Klafyvel/Trace/PCInterface/user_interface.py

# -*- coding: utf-8 -*-

# Form implementation generated from reading ui file 'window.ui'
#
# Created by: PyQt5 UI code generator 5.4.1
#
# WARNING! All changes made in this file will be lost!

from PyQt5 import QtCore, QtGui, QtWidgets

class Ui_MainWindow(object):
    def setupUi(self, MainWindow):
        MainWindow.setObjectName("MainWindow")
        MainWindow.resize(886, 528)
        icon = QtGui.QIcon()
        icon.addPixmap(QtGui.QPixmap("traceIcon.svg"), QtGui.QIcon.Normal, QtGui.QIcon.Off)
        MainWindow.setWindowIcon(icon)
        MainWindow.setTabShape(QtWidgets.QTabWidget.Triangular)
        self.centralwidget = QtWidgets.QWidget(MainWindow)
        self.centralwidget.setObjectName("centralwidget")
        self.verticalLayout_4 = QtWidgets.QVBoxLayout(self.centralwidget)
        self.verticalLayout_4.setObjectName("verticalLayout_4")
        self.tabWidget_2 = QtWidgets.QTabWidget(self.centralwidget)
        self.tabWidget_2.setObjectName("tabWidget_2")
        self.tab_2 = QtWidgets.QWidget()
        self.tab_2.setObjectName("tab_2")
        self.verticalLayout_9 = QtWidgets.QVBoxLayout(self.tab_2)
        self.verticalLayout_9.setObjectName("verticalLayout_9")
        self.horizontalLayout = QtWidgets.QHBoxLayout()
        self.horizontalLayout.setObjectName("horizontalLayout")
        self.filename = QtWidgets.QLabel(self.tab_2)
        self.filename.setObjectName("filename")
        self.horizontalLayout.addWidget(self.filename)
        self.btn_file = QtWidgets.QPushButton(self.tab_2)
        icon1 = QtGui.QIcon()
        icon1.addPixmap(QtGui.QPixmap("load.png"), QtGui.QIcon.Normal, QtGui.QIcon.Off)
        self.btn_file.setIcon(icon1)
        self.btn_file.setObjectName("btn_file")
        self.horizontalLayout.addWidget(self.btn_file)
        self.btn_reload = QtWidgets.QPushButton(self.tab_2)
        icon2 = QtGui.QIcon()
        icon2.addPixmap(QtGui.QPixmap("reload.png"), QtGui.QIcon.Normal, QtGui.QIcon.Off)
        self.btn_reload.setIcon(icon2)
        self.btn_reload.setObjectName("btn_reload")
        self.horizontalLayout.addWidget(self.btn_reload)
        self.verticalLayout_9.addLayout(self.horizontalLayout)
        self.btn_preprocessor = QtWidgets.QPushButton(self.tab_2)
        icon3 = QtGui.QIcon()
        icon3.addPixmap(QtGui.QPixmap("work.png"), QtGui.QIcon.Normal, QtGui.QIcon.Off)
        self.btn_preprocessor.setIcon(icon3)
        self.btn_preprocessor.setObjectName("btn_preprocessor")
        self.verticalLayout_9.addWidget(self.btn_preprocessor)
        self.widget_2 = QtWidgets.QWidget(self.tab_2)
        self.widget_2.setObjectName("widget_2")
        self.horizontalLayout_5 = QtWidgets.QHBoxLayout(self.widget_2)
        self.horizontalLayout_5.setContentsMargins(0, 0, 0, 0)
        self.horizontalLayout_5.setObjectName("horizontalLayout_5")
        self.widget = QtWidgets.QWidget(self.widget_2)
        self.widget.setObjectName("widget")
        self.verticalLayout_5 = QtWidgets.QVBoxLayout(self.widget)
        self.verticalLayout_5.setContentsMargins(0, 0, 0, 0)
        self.verticalLayout_5.setObjectName("verticalLayout_5")
        self.fileview = QtWidgets.QGraphicsView(self.widget)
        self.fileview.setSizeAdjustPolicy(QtWidgets.QAbstractScrollArea.AdjustToContents)
        self.fileview.setDragMode(QtWidgets.QGraphicsView.ScrollHandDrag)
        self.fileview.setObjectName("fileview")
        self.verticalLayout_5.addWidget(self.fileview)
        self.widget_5 = QtWidgets.QWidget(self.widget)
        self.widget_5.setObjectName("widget_5")
        self.horizontalLayout_8 = QtWidgets.QHBoxLayout(self.widget_5)
        self.horizontalLayout_8.setContentsMargins(0, 0, 0, 0)
        self.horizontalLayout_8.setObjectName("horizontalLayout_8")
        self.display_draw_steps = QtWidgets.QCheckBox(self.widget_5)
        self.display_draw_steps.setObjectName("display_draw_steps")
        self.horizontalLayout_8.addWidget(self.display_draw_steps)
        self.redraw = QtWidgets.QPushButton(self.widget_5)
        icon4 = QtGui.QIcon()
        icon4.addPixmap(QtGui.QPixmap("writing.png"), QtGui.QIcon.Normal, QtGui.QIcon.Off)
        self.redraw.setIcon(icon4)
        self.redraw.setObjectName("redraw")
        self.horizontalLayout_8.addWidget(self.redraw)
        self.verticalLayout_5.addWidget(self.widget_5)
        self.horizontalLayout_5.addWidget(self.widget)
        self.widget_3 = QtWidgets.QWidget(self.widget_2)
        self.widget_3.setObjectName("widget_3")
        self.verticalLayout = QtWidgets.QVBoxLayout(self.widget_3)
        self.verticalLayout.setContentsMargins(0, 0, 0, 0)
        self.verticalLayout.setObjectName("verticalLayout")
        self.code_edit = QtWidgets.QTextEdit(self.widget_3)
        self.code_edit.setObjectName("code_edit")
        self.verticalLayout.addWidget(self.code_edit)
        self.widget_4 = QtWidgets.QWidget(self.widget_3)
        self.widget_4.setObjectName("widget_4")
        self.horizontalLayout_7 = QtWidgets.QHBoxLayout(self.widget_4)
        self.horizontalLayout_7.setContentsMargins(0, 0, 0, 0)
        self.horizontalLayout_7.setObjectName("horizontalLayout_7")
        self.btn_save_file = QtWidgets.QPushButton(self.widget_4)
        icon5 = QtGui.QIcon()
        icon5.addPixmap(QtGui.QPixmap("save.png"), QtGui.QIcon.Normal, QtGui.QIcon.Off)
        self.btn_save_file.setIcon(icon5)
        self.btn_save_file.setObjectName("btn_save_file")
        self.horizontalLayout_7.addWidget(self.btn_save_file)
        self.btn_save_as = QtWidgets.QPushButton(self.widget_4)
        self.btn_save_as.setIcon(icon5)
        self.btn_save_as.setObjectName("btn_save_as")
        self.horizontalLayout_7.addWidget(self.btn_save_as)
        self.verticalLayout.addWidget(self.widget_4)
        self.horizontalLayout_5.addWidget(self.widget_3)
        self.verticalLayout_9.addWidget(self.widget_2)
        self.tabWidget_2.addTab(self.tab_2, "")
        self.tab_3 = QtWidgets.QWidget()
        self.tab_3.setObjectName("tab_3")
        self.horizontalLayout_2 = QtWidgets.QHBoxLayout(self.tab_3)
        self.horizontalLayout_2.setObjectName("horizontalLayout_2")
        self.groupBox = QtWidgets.QGroupBox(self.tab_3)
        self.groupBox.setObjectName("groupBox")
        self.verticalLayout_2 = QtWidgets.QVBoxLayout(self.groupBox)
        self.verticalLayout_2.setObjectName("verticalLayout_2")
        self.serial_monitor = QtWidgets.QTextEdit(self.groupBox)
        sizePolicy = QtWidgets.QSizePolicy(QtWidgets.QSizePolicy.Expanding, QtWidgets.QSizePolicy.Minimum)
        sizePolicy.setHorizontalStretch(0)
        sizePolicy.setVerticalStretch(0)
        sizePolicy.setHeightForWidth(self.serial_monitor.sizePolicy().hasHeightForWidth())
        self.serial_monitor.setSizePolicy(sizePolicy)
        self.serial_monitor.setMinimumSize(QtCore.QSize(0, 300))
        self.serial_monitor.setMaximumSize(QtCore.QSize(16777215, 2000))
        self.serial_monitor.setStyleSheet("background-color:black;")
        self.serial_monitor.setReadOnly(True)
        self.serial_monitor.setObjectName("serial_monitor")
        self.verticalLayout_2.addWidget(self.serial_monitor)
        self.horizontalLayout_4 = QtWidgets.QHBoxLayout()
        self.horizontalLayout_4.setObjectName("horizontalLayout_4")
        self.label_4 = QtWidgets.QLabel(self.groupBox)
        self.label_4.setObjectName("label_4")
        self.horizontalLayout_4.addWidget(self.label_4)
        self.command_edit = QtWidgets.QLineEdit(self.groupBox)
        self.command_edit.setObjectName("command_edit")
        self.horizontalLayout_4.addWidget(self.command_edit)
        self.btn_command = QtWidgets.QPushButton(self.groupBox)
        icon6 = QtGui.QIcon()
        icon6.addPixmap(QtGui.QPixmap("run.png"), QtGui.QIcon.Normal, QtGui.QIcon.Off)
        self.btn_command.setIcon(icon6)
        self.btn_command.setObjectName("btn_command")
        self.horizontalLayout_4.addWidget(self.btn_command)
        self.verticalLayout_2.addLayout(self.horizontalLayout_4)
        self.horizontalLayout_2.addWidget(self.groupBox)
        self.tabWidget = QtWidgets.QTabWidget(self.tab_3)
        self.tabWidget.setObjectName("tabWidget")
        self.tab_serie = QtWidgets.QWidget()
        self.tab_serie.setObjectName("tab_serie")
        self.verticalLayout_3 = QtWidgets.QVBoxLayout(self.tab_serie)
        self.verticalLayout_3.setObjectName("verticalLayout_3")
        self.chk_enableFakeSerial = QtWidgets.QCheckBox(self.tab_serie)
        self.chk_enableFakeSerial.setObjectName("chk_enableFakeSerial")
        self.verticalLayout_3.addWidget(self.chk_enableFakeSerial)
        self.trueSerialContainer = QtWidgets.QWidget(self.tab_serie)
        self.trueSerialContainer.setObjectName("trueSerialContainer")
        self.verticalLayout_10 = QtWidgets.QVBoxLayout(self.trueSerialContainer)
        self.verticalLayout_10.setContentsMargins(0, 0, 0, 0)
        self.verticalLayout_10.setObjectName("verticalLayout_10")
        self.serial_settings = QtWidgets.QFormLayout()
        self.serial_settings.setObjectName("serial_settings")
        self.label = QtWidgets.QLabel(self.trueSerialContainer)
        self.label.setObjectName("label")
        self.serial_settings.setWidget(0, QtWidgets.QFormLayout.LabelRole, self.label)
        self.baudrate = QtWidgets.QComboBox(self.trueSerialContainer)
        self.baudrate.setObjectName("baudrate")
        self.baudrate.addItem("")
        self.baudrate.addItem("")
        self.baudrate.addItem("")
        self.baudrate.addItem("")
        self.baudrate.addItem("")
        self.baudrate.addItem("")
        self.baudrate.addItem("")
        self.baudrate.addItem("")
        self.baudrate.addItem("")
        self.baudrate.addItem("")
        self.baudrate.addItem("")
        self.serial_settings.setWidget(0, QtWidgets.QFormLayout.FieldRole, self.baudrate)
        self.portSRieLabel = QtWidgets.QLabel(self.trueSerialContainer)
        self.portSRieLabel.setObjectName("portSRieLabel")
        self.serial_settings.setWidget(1, QtWidgets.QFormLayout.LabelRole, self.portSRieLabel)
        self.serial_ports_list = QtWidgets.QComboBox(self.trueSerialContainer)
        self.serial_ports_list.setObjectName("serial_ports_list")
        self.serial_settings.setWidget(1, QtWidgets.QFormLayout.FieldRole, self.serial_ports_list)
        self.btn_serial_ports_list = QtWidgets.QPushButton(self.trueSerialContainer)
        self.btn_serial_ports_list.setObjectName("btn_serial_ports_list")
        self.serial_settings.setWidget(2, QtWidgets.QFormLayout.FieldRole, self.btn_serial_ports_list)
        self.label_5 = QtWidgets.QLabel(self.trueSerialContainer)
        self.label_5.setObjectName("label_5")
        self.serial_settings.setWidget(3, QtWidgets.QFormLayout.LabelRole, self.label_5)
        self.timeout_read = QtWidgets.QSpinBox(self.trueSerialContainer)
        self.timeout_read.setMaximum(1000)
        self.timeout_read.setProperty("value", 10)
        self.timeout_read.setObjectName("timeout_read")
        self.serial_settings.setWidget(3, QtWidgets.QFormLayout.FieldRole, self.timeout_read)
        self.utiliserFichierLogTxtLabel = QtWidgets.QLabel(self.trueSerialContainer)
        self.utiliserFichierLogTxtLabel.setObjectName("utiliserFichierLogTxtLabel")
        self.serial_settings.setWidget(4, QtWidgets.QFormLayout.LabelRole, self.utiliserFichierLogTxtLabel)
        self.use_log = QtWidgets.QCheckBox(self.trueSerialContainer)
        self.use_log.setObjectName("use_log")
        self.serial_settings.setWidget(4, QtWidgets.QFormLayout.FieldRole, self.use_log)
        self.verticalLayout_10.addLayout(self.serial_settings)
        self.btn_connect = QtWidgets.QPushButton(self.trueSerialContainer)
        icon7 = QtGui.QIcon()
        icon7.addPixmap(QtGui.QPixmap("connect.png"), QtGui.QIcon.Normal, QtGui.QIcon.Off)
        self.btn_connect.setIcon(icon7)
        self.btn_connect.setObjectName("btn_connect")
        self.verticalLayout_10.addWidget(self.btn_connect)
        self.verticalLayout_3.addWidget(self.trueSerialContainer)
        self.tabWidget.addTab(self.tab_serie, "")
        self.tab = QtWidgets.QWidget()
        self.tab.setObjectName("tab")
        self.verticalLayout_8 = QtWidgets.QVBoxLayout(self.tab)
        self.verticalLayout_8.setObjectName("verticalLayout_8")
        self.send_manual_cmd = QtWidgets.QCheckBox(self.tab)
        self.send_manual_cmd.setObjectName("send_manual_cmd")
        self.verticalLayout_8.addWidget(self.send_manual_cmd)
        self.grp_plan = QtWidgets.QGroupBox(self.tab)
        self.grp_plan.setObjectName("grp_plan")
        self.verticalLayout_6 = QtWidgets.QVBoxLayout(self.grp_plan)
        self.verticalLayout_6.setObjectName("verticalLayout_6")
        self.gridLayout_2 = QtWidgets.QGridLayout()
        self.gridLayout_2.setObjectName("gridLayout_2")
        self.btn_y_plus = QtWidgets.QPushButton(self.grp_plan)
        icon8 = QtGui.QIcon()
        icon8.addPixmap(QtGui.QPixmap("up.png"), QtGui.QIcon.Normal, QtGui.QIcon.Off)
        self.btn_y_plus.setIcon(icon8)
        self.btn_y_plus.setObjectName("btn_y_plus")
        self.gridLayout_2.addWidget(self.btn_y_plus, 0, 1, 1, 1)
        self.btn_x_plus = QtWidgets.QPushButton(self.grp_plan)
        icon9 = QtGui.QIcon()
        icon9.addPixmap(QtGui.QPixmap("right.png"), QtGui.QIcon.Normal, QtGui.QIcon.Off)
        self.btn_x_plus.setIcon(icon9)
        self.btn_x_plus.setObjectName("btn_x_plus")
        self.gridLayout_2.addWidget(self.btn_x_plus, 1, 2, 1, 1)
        self.btn_y_minus = QtWidgets.QPushButton(self.grp_plan)
        icon10 = QtGui.QIcon()
        icon10.addPixmap(QtGui.QPixmap("down.png"), QtGui.QIcon.Normal, QtGui.QIcon.Off)
        self.btn_y_minus.setIcon(icon10)
        self.btn_y_minus.setObjectName("btn_y_minus")
        self.gridLayout_2.addWidget(self.btn_y_minus, 2, 1, 1, 1)
        self.label_6 = QtWidgets.QLabel(self.grp_plan)
        self.label_6.setObjectName("label_6")
        self.gridLayout_2.addWidget(self.label_6, 0, 3, 1, 1)
        self.btn_x_minus = QtWidgets.QPushButton(self.grp_plan)
        icon11 = QtGui.QIcon()
        icon11.addPixmap(QtGui.QPixmap("left.png"), QtGui.QIcon.Normal, QtGui.QIcon.Off)
        self.btn_x_minus.setIcon(icon11)
        self.btn_x_minus.setObjectName("btn_x_minus")
        self.gridLayout_2.addWidget(self.btn_x_minus, 1, 0, 1, 1)
        self.step_x = QtWidgets.QDoubleSpinBox(self.grp_plan)
        self.step_x.setPrefix("")
        self.step_x.setProperty("value", 1.0)
        self.step_x.setObjectName("step_x")
        self.gridLayout_2.addWidget(self.step_x, 0, 4, 1, 1)
        self.label_7 = QtWidgets.QLabel(self.grp_plan)
        self.label_7.setObjectName("label_7")
        self.gridLayout_2.addWidget(self.label_7, 2, 3, 1, 1)
        self.step_y = QtWidgets.QDoubleSpinBox(self.grp_plan)
        self.step_y.setProperty("value", 1.0)
        self.step_y.setObjectName("step_y")
        self.gridLayout_2.addWidget(self.step_y, 2, 4, 1, 1)
        self.verticalLayout_6.addLayout(self.gridLayout_2)
        self.verticalLayout_8.addWidget(self.grp_plan)
        self.horizontalLayout_3 = QtWidgets.QHBoxLayout()
        self.horizontalLayout_3.setObjectName("horizontalLayout_3")
        self.grp_z = QtWidgets.QGroupBox(self.tab)
        self.grp_z.setFlat(False)
        self.grp_z.setCheckable(False)
        self.grp_z.setObjectName("grp_z")
        self.horizontalLayout_6 = QtWidgets.QHBoxLayout(self.grp_z)
        self.horizontalLayout_6.setObjectName("horizontalLayout_6")
        self.btn_set_z_low = QtWidgets.QPushButton(self.grp_z)
        self.btn_set_z_low.setIcon(icon4)
        self.btn_set_z_low.setIconSize(QtCore.QSize(64, 64))
        self.btn_set_z_low.setObjectName("btn_set_z_low")
        self.horizontalLayout_6.addWidget(self.btn_set_z_low)
        self.btn_set_z_high = QtWidgets.QPushButton(self.grp_z)
        icon12 = QtGui.QIcon()
        icon12.addPixmap(QtGui.QPixmap("not_writing.png"), QtGui.QIcon.Normal, QtGui.QIcon.Off)
        self.btn_set_z_high.setIcon(icon12)
        self.btn_set_z_high.setIconSize(QtCore.QSize(64, 64))
        self.btn_set_z_high.setObjectName("btn_set_z_high")
        self.horizontalLayout_6.addWidget(self.btn_set_z_high)
        self.horizontalLayout_3.addWidget(self.grp_z)
        self.verticalLayout_8.addLayout(self.horizontalLayout_3)
        self.btn_go_to_zero = QtWidgets.QPushButton(self.tab)
        sizePolicy = QtWidgets.QSizePolicy(QtWidgets.QSizePolicy.Expanding, QtWidgets.QSizePolicy.Expanding)
        sizePolicy.setHorizontalStretch(0)
        sizePolicy.setVerticalStretch(0)
        sizePolicy.setHeightForWidth(self.btn_go_to_zero.sizePolicy().hasHeightForWidth())
        self.btn_go_to_zero.setSizePolicy(sizePolicy)
        icon13 = QtGui.QIcon()
        icon13.addPixmap(QtGui.QPixmap("origin.png"), QtGui.QIcon.Normal, QtGui.QIcon.Off)
        self.btn_go_to_zero.setIcon(icon13)
        self.btn_go_to_zero.setIconSize(QtCore.QSize(64, 64))
        self.btn_go_to_zero.setFlat(False)
        self.btn_go_to_zero.setObjectName("btn_go_to_zero")
        self.verticalLayout_8.addWidget(self.btn_go_to_zero)
        self.btn_send_current_file = QtWidgets.QPushButton(self.tab)
        icon14 = QtGui.QIcon()
        icon14.addPixmap(QtGui.QPixmap("upload.png"), QtGui.QIcon.Normal, QtGui.QIcon.Off)
        self.btn_send_current_file.setIcon(icon14)
        self.btn_send_current_file.setObjectName("btn_send_current_file")
        self.verticalLayout_8.addWidget(self.btn_send_current_file)
        self.tabWidget.addTab(self.tab, "")
        self.horizontalLayout_2.addWidget(self.tabWidget)
        self.tabWidget_2.addTab(self.tab_3, "")
        self.tab_4 = QtWidgets.QWidget()
        self.tab_4.setObjectName("tab_4")
        self.verticalLayout_7 = QtWidgets.QVBoxLayout(self.tab_4)
        self.verticalLayout_7.setObjectName("verticalLayout_7")
        self.label_2 = QtWidgets.QLabel(self.tab_4)
        self.label_2.setTextFormat(QtCore.Qt.RichText)
        self.label_2.setObjectName("label_2")
        self.verticalLayout_7.addWidget(self.label_2)
        self.textBrowser_2 = QtWidgets.QTextBrowser(self.tab_4)
        self.textBrowser_2.setObjectName("textBrowser_2")
        self.verticalLayout_7.addWidget(self.textBrowser_2)
        self.aboutQt = QtWidgets.QPushButton(self.tab_4)
        icon = QtGui.QIcon.fromTheme("Qt")
        self.aboutQt.setIcon(icon)
        self.aboutQt.setObjectName("aboutQt")
        self.verticalLayout_7.addWidget(self.aboutQt)
        self.tabWidget_2.addTab(self.tab_4, "")
        self.verticalLayout_4.addWidget(self.tabWidget_2)
        MainWindow.setCentralWidget(self.centralwidget)
        self.actionSave = QtWidgets.QAction(MainWindow)
        self.actionSave.setObjectName("actionSave")
        self.actionSaveAs = QtWidgets.QAction(MainWindow)
        self.actionSaveAs.setObjectName("actionSaveAs")
        self.actionRedraw = QtWidgets.QAction(MainWindow)
        self.actionRedraw.setObjectName("actionRedraw")
        self.actionReload = QtWidgets.QAction(MainWindow)
        self.actionReload.setObjectName("actionReload")

        self.retranslateUi(MainWindow)
        self.tabWidget_2.setCurrentIndex(0)
        self.tabWidget.setCurrentIndex(0)
        self.baudrate.setCurrentIndex(4)
        self.command_edit.returnPressed.connect(self.btn_command.click)
        QtCore.QMetaObject.connectSlotsByName(MainWindow)

    def retranslateUi(self, MainWindow):
        _translate = QtCore.QCoreApplication.translate
        MainWindow.setWindowTitle(_translate("MainWindow", "Trace"))
        self.filename.setText(_translate("MainWindow", "Pas de fichier"))
        self.btn_file.setText(_translate("MainWindow", "Choisir le fichier"))
        self.btn_reload.setText(_translate("MainWindow", "Recharger"))
        self.btn_preprocessor.setText(_translate("MainWindow", "Utiliser le préprocesseur sur le fichier"))
        self.display_draw_steps.setText(_translate("MainWindow", "Afficher les étapes"))
        self.redraw.setText(_translate("MainWindow", "Redessiner"))
        self.btn_save_file.setText(_translate("MainWindow", "Enregistrer"))
        self.btn_save_as.setText(_translate("MainWindow", "Enregister sous..."))
        self.tabWidget_2.setTabText(self.tabWidget_2.indexOf(self.tab_2), _translate("MainWindow", "Fichier"))
        self.groupBox.setTitle(_translate("MainWindow", "Moniteur série"))
        self.serial_monitor.setHtml(_translate("MainWindow", "<!DOCTYPE HTML PUBLIC \"-//W3C//DTD HTML 4.0//EN\" \"http://www.w3.org/TR/REC-html40/strict.dtd\">\n"
"<html><head><meta name=\"qrichtext\" content=\"1\" /><style type=\"text/css\">\n"
"p, li { white-space: pre-wrap; }\n"
"</style></head><body style=\" font-family:\'Ubuntu\'; font-size:11pt; font-weight:400; font-style:normal;\">\n"
"<p style=\"-qt-paragraph-type:empty; margin-top:12px; margin-bottom:12px; margin-left:0px; margin-right:0px; -qt-block-indent:0; text-indent:0px;\"><br /></p></body></html>"))
        self.label_4.setText(_translate("MainWindow", "Commande :"))
        self.btn_command.setText(_translate("MainWindow", "Envoyer"))
        self.chk_enableFakeSerial.setText(_translate("MainWindow", "Simuler un port série"))
        self.label.setText(_translate("MainWindow", "Baudrate"))
        self.baudrate.setItemText(0, _translate("MainWindow", "300"))
        self.baudrate.setItemText(1, _translate("MainWindow", "1200"))
        self.baudrate.setItemText(2, _translate("MainWindow", "2400"))
        self.baudrate.setItemText(3, _translate("MainWindow", "4800"))
        self.baudrate.setItemText(4, _translate("MainWindow", "9600"))
        self.baudrate.setItemText(5, _translate("MainWindow", "19200"))
        self.baudrate.setItemText(6, _translate("MainWindow", "38400"))
        self.baudrate.setItemText(7, _translate("MainWindow", "57600"))
        self.baudrate.setItemText(8, _translate("MainWindow", "115200"))
        self.baudrate.setItemText(9, _translate("MainWindow", "230400"))
        self.baudrate.setItemText(10, _translate("MainWindow", "250000"))
        self.portSRieLabel.setText(_translate("MainWindow", "Port série"))
        self.btn_serial_ports_list.setText(_translate("MainWindow", "Lister les ports série"))
        self.label_5.setText(_translate("MainWindow", "Timeout (ms)"))
        self.utiliserFichierLogTxtLabel.setText(_translate("MainWindow", "Utiliser fichier log.txt"))
        self.btn_connect.setText(_translate("MainWindow", "Connecter"))
        self.tabWidget.setTabText(self.tabWidget.indexOf(self.tab_serie), _translate("MainWindow", "Port série"))
        self.send_manual_cmd.setText(_translate("MainWindow", "Envoi de commandes manuelles"))
        self.grp_plan.setTitle(_translate("MainWindow", "Position dans le plan"))
        self.btn_y_plus.setText(_translate("MainWindow", "Y+"))
        self.btn_x_plus.setText(_translate("MainWindow", "X+"))
        self.btn_y_minus.setText(_translate("MainWindow", "Y-"))
        self.label_6.setText(_translate("MainWindow", "Pas x :"))
        self.btn_x_minus.setText(_translate("MainWindow", "X-"))
        self.step_x.setSuffix(_translate("MainWindow", " mm"))
        self.label_7.setText(_translate("MainWindow", "Pas y :"))
        self.step_y.setSuffix(_translate("MainWindow", " mm"))
        self.grp_z.setTitle(_translate("MainWindow", "Axe Z"))
        self.btn_set_z_low.setText(_translate("MainWindow", "Position basse"))
        self.btn_set_z_high.setText(_translate("MainWindow", "Position haute"))
        self.btn_go_to_zero.setText(_translate("MainWindow", "Aller à la position\n"
"Zéro"))
        self.btn_send_current_file.setText(_translate("MainWindow", "Envoyer le fichier courrant"))
        self.tabWidget.setTabText(self.tabWidget.indexOf(self.tab), _translate("MainWindow", "Contrôles"))
        self.tabWidget_2.setTabText(self.tabWidget_2.indexOf(self.tab_3), _translate("MainWindow", "Port Série"))
        self.label_2.setText(_translate("MainWindow", "<!DOCTYPE HTML PUBLIC \"-//W3C//DTD HTML 4.0//EN\" \"http://www.w3.org/TR/REC-html40/strict.dtd\">\n"
"<html><head><meta name=\"qrichtext\" content=\"1\" /><style type=\"text/css\">\n"
"p, li { white-space: pre-wrap; }\n"
"</style></head><body style=\" font-family:\'Ubuntu\'; font-size:11pt; font-weight:400; font-style:normal;\">\n"
"<p style=\" margin-top:0px; margin-bottom:0px; margin-left:0px; margin-right:0px; -qt-block-indent:0; text-indent:0px;\">Trace est un logiciel écrit par <span style=\" font-weight:600;\">Hugo LEVY-FALK </span>(klafyvel), disponible sous la license <a href=\"http://www.gnu.org/licenses/\"><span style=\" text-decoration: underline; color:#0000ff;\">GNU GPL</span></a>  . </p>\n"
"<p style=\" margin-top:0px; margin-bottom:0px; margin-left:0px; margin-right:0px; -qt-block-indent:0; text-indent:0px;\">Il s\'agit d\'un utilitaire agissant en tant qu\'intermédiaire entre une machine interprétant du GCode et un opérateur.</p>\n"
"<p style=\" margin-top:0px; margin-bottom:0px; margin-left:0px; margin-right:0px; -qt-block-indent:0; text-indent:0px;\">Pour en savoir plus, consulter le site <a href=\"http://sivigik.com\"><span style=\" text-decoration: underline; color:#0000ff;\">Sivigik</span></a>.</p>\n"
"<p style=\"-qt-paragraph-type:empty; margin-top:0px; margin-bottom:0px; margin-left:0px; margin-right:0px; -qt-block-indent:0; text-indent:0px;\"><br /></p>\n"
"<p style=\" margin-top:0px; margin-bottom:0px; margin-left:0px; margin-right:0px; -qt-block-indent:0; text-indent:0px;\">Trace s\'appuit sur le Framework Qt au travers de la bibliothèque PyQt5 et est développé en Python3.</p></body></html>"))
        self.textBrowser_2.setHtml(_translate("MainWindow", "<!DOCTYPE HTML PUBLIC \"-//W3C//DTD HTML 4.0//EN\" \"http://www.w3.org/TR/REC-html40/strict.dtd\">\n"
"<html><head><meta name=\"qrichtext\" content=\"1\" /><title>GNU General Public License v3.0 - GNU Project - Free Software Foundation (FSF)</title><style type=\"text/css\">\n"
"p, li { white-space: pre-wrap; }\n"
"</style></head><body style=\" font-family:\'Ubuntu\'; font-size:11pt; font-weight:400; font-style:normal;\">\n"
"<p style=\" margin-top:14px; margin-bottom:12px; margin-left:0px; margin-right:0px; -qt-block-indent:0; text-indent:0px;\"><span style=\" font-size:large; font-weight:600;\">GNU GENERAL PUBLIC LICENSE</span></p>\n"
"<p style=\" margin-top:12px; margin-bottom:12px; margin-left:0px; margin-right:0px; -qt-block-indent:0; text-indent:0px;\">Version 3, 29 June 2007 </p>\n"
"<p style=\" margin-top:12px; margin-bottom:12px; margin-left:0px; margin-right:0px; -qt-block-indent:0; text-indent:0px;\">Copyright © 2007 Free Software Foundation, Inc. &lt;<a href=\"http://fsf.org/\"><span style=\" text-decoration: underline; color:#0000ff;\">http://fsf.org/</span></a>&gt;</p>\n"
"<p style=\" margin-top:12px; margin-bottom:12px; margin-left:0px; margin-right:0px; -qt-block-indent:0; text-indent:0px;\">Everyone is permitted to copy and distribute verbatim copies of this license document, but changing it is not allowed. </p>\n"
"<p style=\" margin-top:14px; margin-bottom:12px; margin-left:0px; margin-right:0px; -qt-block-indent:0; text-indent:0px;\"><a name=\"preamble\"></a><span style=\" font-size:large; font-weight:600;\">P</span><span style=\" font-size:large; font-weight:600;\">reamble</span> </p>\n"
"<p style=\" margin-top:12px; margin-bottom:12px; margin-left:0px; margin-right:0px; -qt-block-indent:0; text-indent:0px;\">The GNU General Public License is a free, copyleft license for software and other kinds of works. </p>\n"
"<p style=\" margin-top:12px; margin-bottom:12px; margin-left:0px; margin-right:0px; -qt-block-indent:0; text-indent:0px;\">The licenses for most software and other practical works are designed to take away your freedom to share and change the works. By contrast, the GNU General Public License is intended to guarantee your freedom to share and change all versions of a program--to make sure it remains free software for all its users. We, the Free Software Foundation, use the GNU General Public License for most of our software; it applies also to any other work released this way by its authors. You can apply it to your programs, too. </p>\n"
"<p style=\" margin-top:12px; margin-bottom:12px; margin-left:0px; margin-right:0px; -qt-block-indent:0; text-indent:0px;\">When we speak of free software, we are referring to freedom, not price. Our General Public Licenses are designed to make sure that you have the freedom to distribute copies of free software (and charge for them if you wish), that you receive source code or can get it if you want it, that you can change the software or use pieces of it in new free programs, and that you know you can do these things. </p>\n"
"<p style=\" margin-top:12px; margin-bottom:12px; margin-left:0px; margin-right:0px; -qt-block-indent:0; text-indent:0px;\">To protect your rights, we need to prevent others from denying you these rights or asking you to surrender the rights. Therefore, you have certain responsibilities if you distribute copies of the software, or if you modify it: responsibilities to respect the freedom of others. </p>\n"
"<p style=\" margin-top:12px; margin-bottom:12px; margin-left:0px; margin-right:0px; -qt-block-indent:0; text-indent:0px;\">For example, if you distribute copies of such a program, whether gratis or for a fee, you must pass on to the recipients the same freedoms that you received. You must make sure that they, too, receive or can get the source code. And you must show them these terms so they know their rights. </p>\n"
"<p style=\" margin-top:12px; margin-bottom:12px; margin-left:0px; margin-right:0px; -qt-block-indent:0; text-indent:0px;\">Developers that use the GNU GPL protect your rights with two steps: (1) assert copyright on the software, and (2) offer you this License giving you legal permission to copy, distribute and/or modify it. </p>\n"
"<p style=\" margin-top:12px; margin-bottom:12px; margin-left:0px; margin-right:0px; -qt-block-indent:0; text-indent:0px;\">For the developers\' and authors\' protection, the GPL clearly explains that there is no warranty for this free software. For both users\' and authors\' sake, the GPL requires that modified versions be marked as changed, so that their problems will not be attributed erroneously to authors of previous versions. </p>\n"
"<p style=\" margin-top:12px; margin-bottom:12px; margin-left:0px; margin-right:0px; -qt-block-indent:0; text-indent:0px;\">Some devices are designed to deny users access to install or run modified versions of the software inside them, although the manufacturer can do so. This is fundamentally incompatible with the aim of protecting users\' freedom to change the software. The systematic pattern of such abuse occurs in the area of products for individuals to use, which is precisely where it is most unacceptable. Therefore, we have designed this version of the GPL to prohibit the practice for those products. If such problems arise substantially in other domains, we stand ready to extend this provision to those domains in future versions of the GPL, as needed to protect the freedom of users. </p>\n"
"<p style=\" margin-top:12px; margin-bottom:12px; margin-left:0px; margin-right:0px; -qt-block-indent:0; text-indent:0px;\">Finally, every program is threatened constantly by software patents. States should not allow patents to restrict development and use of software on general-purpose computers, but in those that do, we wish to avoid the special danger that patents applied to a free program could make it effectively proprietary. To prevent this, the GPL assures that patents cannot be used to render the program non-free. </p>\n"
"<p style=\" margin-top:12px; margin-bottom:12px; margin-left:0px; margin-right:0px; -qt-block-indent:0; text-indent:0px;\">The precise terms and conditions for copying, distribution and modification follow. </p>\n"
"<p style=\" margin-top:14px; margin-bottom:12px; margin-left:0px; margin-right:0px; -qt-block-indent:0; text-indent:0px;\"><a name=\"terms\"></a><span style=\" font-size:large; font-weight:600;\">T</span><span style=\" font-size:large; font-weight:600;\">ERMS AND CONDITIONS</span> </p>\n"
"<p style=\" margin-top:12px; margin-bottom:12px; margin-left:0px; margin-right:0px; -qt-block-indent:0; text-indent:0px;\"><a name=\"section0\"></a><span style=\" font-size:medium; font-weight:600;\">0</span><span style=\" font-size:medium; font-weight:600;\">. Definitions.</span> </p>\n"
"<p style=\" margin-top:12px; margin-bottom:12px; margin-left:0px; margin-right:0px; -qt-block-indent:0; text-indent:0px;\">“This License” refers to version 3 of the GNU General Public License. </p>\n"
"<p style=\" margin-top:12px; margin-bottom:12px; margin-left:0px; margin-right:0px; -qt-block-indent:0; text-indent:0px;\">“Copyright” also means copyright-like laws that apply to other kinds of works, such as semiconductor masks. </p>\n"
"<p style=\" margin-top:12px; margin-bottom:12px; margin-left:0px; margin-right:0px; -qt-block-indent:0; text-indent:0px;\">“The Program” refers to any copyrightable work licensed under this License. Each licensee is addressed as “you”. “Licensees” and “recipients” may be individuals or organizations. </p>\n"
"<p style=\" margin-top:12px; margin-bottom:12px; margin-left:0px; margin-right:0px; -qt-block-indent:0; text-indent:0px;\">To “modify” a work means to copy from or adapt all or part of the work in a fashion requiring copyright permission, other than the making of an exact copy. The resulting work is called a “modified version” of the earlier work or a work “based on” the earlier work. </p>\n"
"<p style=\" margin-top:12px; margin-bottom:12px; margin-left:0px; margin-right:0px; -qt-block-indent:0; text-indent:0px;\">A “covered work” means either the unmodified Program or a work based on the Program. </p>\n"
"<p style=\" margin-top:12px; margin-bottom:12px; margin-left:0px; margin-right:0px; -qt-block-indent:0; text-indent:0px;\">To “propagate” a work means to do anything with it that, without permission, would make you directly or secondarily liable for infringement under applicable copyright law, except executing it on a computer or modifying a private copy. Propagation includes copying, distribution (with or without modification), making available to the public, and in some countries other activities as well. </p>\n"
"<p style=\" margin-top:12px; margin-bottom:12px; margin-left:0px; margin-right:0px; -qt-block-indent:0; text-indent:0px;\">To “convey” a work means any kind of propagation that enables other parties to make or receive copies. Mere interaction with a user through a computer network, with no transfer of a copy, is not conveying. </p>\n"
"<p style=\" margin-top:12px; margin-bottom:12px; margin-left:0px; margin-right:0px; -qt-block-indent:0; text-indent:0px;\">An interactive user interface displays “Appropriate Legal Notices” to the extent that it includes a convenient and prominently visible feature that (1) displays an appropriate copyright notice, and (2) tells the user that there is no warranty for the work (except to the extent that warranties are provided), that licensees may convey the work under this License, and how to view a copy of this License. If the interface presents a list of user commands or options, such as a menu, a prominent item in the list meets this criterion. </p>\n"
"<p style=\" margin-top:12px; margin-bottom:12px; margin-left:0px; margin-right:0px; -qt-block-indent:0; text-indent:0px;\"><a name=\"section1\"></a><span style=\" font-size:medium; font-weight:600;\">1</span><span style=\" font-size:medium; font-weight:600;\">. Source Code.</span> </p>\n"
"<p style=\" margin-top:12px; margin-bottom:12px; margin-left:0px; margin-right:0px; -qt-block-indent:0; text-indent:0px;\">The “source code” for a work means the preferred form of the work for making modifications to it. “Object code” means any non-source form of a work. </p>\n"
"<p style=\" margin-top:12px; margin-bottom:12px; margin-left:0px; margin-right:0px; -qt-block-indent:0; text-indent:0px;\">A “Standard Interface” means an interface that either is an official standard defined by a recognized standards body, or, in the case of interfaces specified for a particular programming language, one that is widely used among developers working in that language. </p>\n"
"<p style=\" margin-top:12px; margin-bottom:12px; margin-left:0px; margin-right:0px; -qt-block-indent:0; text-indent:0px;\">The “System Libraries” of an executable work include anything, other than the work as a whole, that (a) is included in the normal form of packaging a Major Component, but which is not part of that Major Component, and (b) serves only to enable use of the work with that Major Component, or to implement a Standard Interface for which an implementation is available to the public in source code form. A “Major Component”, in this context, means a major essential component (kernel, window system, and so on) of the specific operating system (if any) on which the executable work runs, or a compiler used to produce the work, or an object code interpreter used to run it. </p>\n"
"<p style=\" margin-top:12px; margin-bottom:12px; margin-left:0px; margin-right:0px; -qt-block-indent:0; text-indent:0px;\">The “Corresponding Source” for a work in object code form means all the source code needed to generate, install, and (for an executable work) run the object code and to modify the work, including scripts to control those activities. However, it does not include the work\'s System Libraries, or general-purpose tools or generally available free programs which are used unmodified in performing those activities but which are not part of the work. For example, Corresponding Source includes interface definition files associated with source files for the work, and the source code for shared libraries and dynamically linked subprograms that the work is specifically designed to require, such as by intimate data communication or control flow between those subprograms and other parts of the work. </p>\n"
"<p style=\" margin-top:12px; margin-bottom:12px; margin-left:0px; margin-right:0px; -qt-block-indent:0; text-indent:0px;\">The Corresponding Source need not include anything that users can regenerate automatically from other parts of the Corresponding Source. </p>\n"
"<p style=\" margin-top:12px; margin-bottom:12px; margin-left:0px; margin-right:0px; -qt-block-indent:0; text-indent:0px;\">The Corresponding Source for a work in source code form is that same work. </p>\n"
"<p style=\" margin-top:12px; margin-bottom:12px; margin-left:0px; margin-right:0px; -qt-block-indent:0; text-indent:0px;\"><a name=\"section2\"></a><span style=\" font-size:medium; font-weight:600;\">2</span><span style=\" font-size:medium; font-weight:600;\">. Basic Permissions.</span> </p>\n"
"<p style=\" margin-top:12px; margin-bottom:12px; margin-left:0px; margin-right:0px; -qt-block-indent:0; text-indent:0px;\">All rights granted under this License are granted for the term of copyright on the Program, and are irrevocable provided the stated conditions are met. This License explicitly affirms your unlimited permission to run the unmodified Program. The output from running a covered work is covered by this License only if the output, given its content, constitutes a covered work. This License acknowledges your rights of fair use or other equivalent, as provided by copyright law. </p>\n"
"<p style=\" margin-top:12px; margin-bottom:12px; margin-left:0px; margin-right:0px; -qt-block-indent:0; text-indent:0px;\">You may make, run and propagate covered works that you do not convey, without conditions so long as your license otherwise remains in force. You may convey covered works to others for the sole purpose of having them make modifications exclusively for you, or provide you with facilities for running those works, provided that you comply with the terms of this License in conveying all material for which you do not control copyright. Those thus making or running the covered works for you must do so exclusively on your behalf, under your direction and control, on terms that prohibit them from making any copies of your copyrighted material outside their relationship with you. </p>\n"
"<p style=\" margin-top:12px; margin-bottom:12px; margin-left:0px; margin-right:0px; -qt-block-indent:0; text-indent:0px;\">Conveying under any other circumstances is permitted solely under the conditions stated below. Sublicensing is not allowed; section 10 makes it unnecessary. </p>\n"
"<p style=\" margin-top:12px; margin-bottom:12px; margin-left:0px; margin-right:0px; -qt-block-indent:0; text-indent:0px;\"><a name=\"section3\"></a><span style=\" font-size:medium; font-weight:600;\">3</span><span style=\" font-size:medium; font-weight:600;\">. Protecting Users\' Legal Rights From Anti-Circumvention Law.</span> </p>\n"
"<p style=\" margin-top:12px; margin-bottom:12px; margin-left:0px; margin-right:0px; -qt-block-indent:0; text-indent:0px;\">No covered work shall be deemed part of an effective technological measure under any applicable law fulfilling obligations under article 11 of the WIPO copyright treaty adopted on 20 December 1996, or similar laws prohibiting or restricting circumvention of such measures. </p>\n"
"<p style=\" margin-top:12px; margin-bottom:12px; margin-left:0px; margin-right:0px; -qt-block-indent:0; text-indent:0px;\">When you convey a covered work, you waive any legal power to forbid circumvention of technological measures to the extent such circumvention is effected by exercising rights under this License with respect to the covered work, and you disclaim any intention to limit operation or modification of the work as a means of enforcing, against the work\'s users, your or third parties\' legal rights to forbid circumvention of technological measures. </p>\n"
"<p style=\" margin-top:12px; margin-bottom:12px; margin-left:0px; margin-right:0px; -qt-block-indent:0; text-indent:0px;\"><a name=\"section4\"></a><span style=\" font-size:medium; font-weight:600;\">4</span><span style=\" font-size:medium; font-weight:600;\">. Conveying Verbatim Copies.</span> </p>\n"
"<p style=\" margin-top:12px; margin-bottom:12px; margin-left:0px; margin-right:0px; -qt-block-indent:0; text-indent:0px;\">You may convey verbatim copies of the Program\'s source code as you receive it, in any medium, provided that you conspicuously and appropriately publish on each copy an appropriate copyright notice; keep intact all notices stating that this License and any non-permissive terms added in accord with section 7 apply to the code; keep intact all notices of the absence of any warranty; and give all recipients a copy of this License along with the Program. </p>\n"
"<p style=\" margin-top:12px; margin-bottom:12px; margin-left:0px; margin-right:0px; -qt-block-indent:0; text-indent:0px;\">You may charge any price or no price for each copy that you convey, and you may offer support or warranty protection for a fee. </p>\n"
"<p style=\" margin-top:12px; margin-bottom:12px; margin-left:0px; margin-right:0px; -qt-block-indent:0; text-indent:0px;\"><a name=\"section5\"></a><span style=\" font-size:medium; font-weight:600;\">5</span><span style=\" font-size:medium; font-weight:600;\">. Conveying Modified Source Versions.</span> </p>\n"
"<p style=\" margin-top:12px; margin-bottom:12px; margin-left:0px; margin-right:0px; -qt-block-indent:0; text-indent:0px;\">You may convey a work based on the Program, or the modifications to produce it from the Program, in the form of source code under the terms of section 4, provided that you also meet all of these conditions: </p>\n"
"<ul style=\"margin-top: 0px; margin-bottom: 0px; margin-left: 0px; margin-right: 0px; -qt-list-indent: 1;\"><li style=\" margin-top:12px; margin-bottom:0px; margin-left:0px; margin-right:0px; -qt-block-indent:0; text-indent:0px;\">a) The work must carry prominent notices stating that you modified it, and giving a relevant date. </li>\n"
"<li style=\" margin-top:0px; margin-bottom:0px; margin-left:0px; margin-right:0px; -qt-block-indent:0; text-indent:0px;\">b) The work must carry prominent notices stating that it is released under this License and any conditions added under section 7. This requirement modifies the requirement in section 4 to “keep intact all notices”. </li>\n"
"<li style=\" margin-top:0px; margin-bottom:0px; margin-left:0px; margin-right:0px; -qt-block-indent:0; text-indent:0px;\">c) You must license the entire work, as a whole, under this License to anyone who comes into possession of a copy. This License will therefore apply, along with any applicable section 7 additional terms, to the whole of the work, and all its parts, regardless of how they are packaged. This License gives no permission to license the work in any other way, but it does not invalidate such permission if you have separately received it. </li>\n"
"<li style=\" margin-top:0px; margin-bottom:12px; margin-left:0px; margin-right:0px; -qt-block-indent:0; text-indent:0px;\">d) If the work has interactive user interfaces, each must display Appropriate Legal Notices; however, if the Program has interactive interfaces that do not display Appropriate Legal Notices, your work need not make them do so. </li></ul>\n"
"<p style=\" margin-top:12px; margin-bottom:12px; margin-left:0px; margin-right:0px; -qt-block-indent:0; text-indent:0px;\">A compilation of a covered work with other separate and independent works, which are not by their nature extensions of the covered work, and which are not combined with it such as to form a larger program, in or on a volume of a storage or distribution medium, is called an “aggregate” if the compilation and its resulting copyright are not used to limit the access or legal rights of the compilation\'s users beyond what the individual works permit. Inclusion of a covered work in an aggregate does not cause this License to apply to the other parts of the aggregate. </p>\n"
"<p style=\" margin-top:12px; margin-bottom:12px; margin-left:0px; margin-right:0px; -qt-block-indent:0; text-indent:0px;\"><a name=\"section6\"></a><span style=\" font-size:medium; font-weight:600;\">6</span><span style=\" font-size:medium; font-weight:600;\">. Conveying Non-Source Forms.</span> </p>\n"
"<p style=\" margin-top:12px; margin-bottom:12px; margin-left:0px; margin-right:0px; -qt-block-indent:0; text-indent:0px;\">You may convey a covered work in object code form under the terms of sections 4 and 5, provided that you also convey the machine-readable Corresponding Source under the terms of this License, in one of these ways: </p>\n"
"<ul style=\"margin-top: 0px; margin-bottom: 0px; margin-left: 0px; margin-right: 0px; -qt-list-indent: 1;\"><li style=\" margin-top:12px; margin-bottom:0px; margin-left:0px; margin-right:0px; -qt-block-indent:0; text-indent:0px;\">a) Convey the object code in, or embodied in, a physical product (including a physical distribution medium), accompanied by the Corresponding Source fixed on a durable physical medium customarily used for software interchange. </li>\n"
"<li style=\" margin-top:0px; margin-bottom:0px; margin-left:0px; margin-right:0px; -qt-block-indent:0; text-indent:0px;\">b) Convey the object code in, or embodied in, a physical product (including a physical distribution medium), accompanied by a written offer, valid for at least three years and valid for as long as you offer spare parts or customer support for that product model, to give anyone who possesses the object code either (1) a copy of the Corresponding Source for all the software in the product that is covered by this License, on a durable physical medium customarily used for software interchange, for a price no more than your reasonable cost of physically performing this conveying of source, or (2) access to copy the Corresponding Source from a network server at no charge. </li>\n"
"<li style=\" margin-top:0px; margin-bottom:0px; margin-left:0px; margin-right:0px; -qt-block-indent:0; text-indent:0px;\">c) Convey individual copies of the object code with a copy of the written offer to provide the Corresponding Source. This alternative is allowed only occasionally and noncommercially, and only if you received the object code with such an offer, in accord with subsection 6b. </li>\n"
"<li style=\" margin-top:0px; margin-bottom:0px; margin-left:0px; margin-right:0px; -qt-block-indent:0; text-indent:0px;\">d) Convey the object code by offering access from a designated place (gratis or for a charge), and offer equivalent access to the Corresponding Source in the same way through the same place at no further charge. You need not require recipients to copy the Corresponding Source along with the object code. If the place to copy the object code is a network server, the Corresponding Source may be on a different server (operated by you or a third party) that supports equivalent copying facilities, provided you maintain clear directions next to the object code saying where to find the Corresponding Source. Regardless of what server hosts the Corresponding Source, you remain obligated to ensure that it is available for as long as needed to satisfy these requirements. </li>\n"
"<li style=\" margin-top:0px; margin-bottom:12px; margin-left:0px; margin-right:0px; -qt-block-indent:0; text-indent:0px;\">e) Convey the object code using peer-to-peer transmission, provided you inform other peers where the object code and Corresponding Source of the work are being offered to the general public at no charge under subsection 6d. </li></ul>\n"
"<p style=\" margin-top:12px; margin-bottom:12px; margin-left:0px; margin-right:0px; -qt-block-indent:0; text-indent:0px;\">A separable portion of the object code, whose source code is excluded from the Corresponding Source as a System Library, need not be included in conveying the object code work. </p>\n"
"<p style=\" margin-top:12px; margin-bottom:12px; margin-left:0px; margin-right:0px; -qt-block-indent:0; text-indent:0px;\">A “User Product” is either (1) a “consumer product”, which means any tangible personal property which is normally used for personal, family, or household purposes, or (2) anything designed or sold for incorporation into a dwelling. In determining whether a product is a consumer product, doubtful cases shall be resolved in favor of coverage. For a particular product received by a particular user, “normally used” refers to a typical or common use of that class of product, regardless of the status of the particular user or of the way in which the particular user actually uses, or expects or is expected to use, the product. A product is a consumer product regardless of whether the product has substantial commercial, industrial or non-consumer uses, unless such uses represent the only significant mode of use of the product. </p>\n"
"<p style=\" margin-top:12px; margin-bottom:12px; margin-left:0px; margin-right:0px; -qt-block-indent:0; text-indent:0px;\">“Installation Information” for a User Product means any methods, procedures, authorization keys, or other information required to install and execute modified versions of a covered work in that User Product from a modified version of its Corresponding Source. The information must suffice to ensure that the continued functioning of the modified object code is in no case prevented or interfered with solely because modification has been made. </p>\n"
"<p style=\" margin-top:12px; margin-bottom:12px; margin-left:0px; margin-right:0px; -qt-block-indent:0; text-indent:0px;\">If you convey an object code work under this section in, or with, or specifically for use in, a User Product, and the conveying occurs as part of a transaction in which the right of possession and use of the User Product is transferred to the recipient in perpetuity or for a fixed term (regardless of how the transaction is characterized), the Corresponding Source conveyed under this section must be accompanied by the Installation Information. But this requirement does not apply if neither you nor any third party retains the ability to install modified object code on the User Product (for example, the work has been installed in ROM). </p>\n"
"<p style=\" margin-top:12px; margin-bottom:12px; margin-left:0px; margin-right:0px; -qt-block-indent:0; text-indent:0px;\">The requirement to provide Installation Information does not include a requirement to continue to provide support service, warranty, or updates for a work that has been modified or installed by the recipient, or for the User Product in which it has been modified or installed. Access to a network may be denied when the modification itself materially and adversely affects the operation of the network or violates the rules and protocols for communication across the network. </p>\n"
"<p style=\" margin-top:12px; margin-bottom:12px; margin-left:0px; margin-right:0px; -qt-block-indent:0; text-indent:0px;\">Corresponding Source conveyed, and Installation Information provided, in accord with this section must be in a format that is publicly documented (and with an implementation available to the public in source code form), and must require no special password or key for unpacking, reading or copying. </p>\n"
"<p style=\" margin-top:12px; margin-bottom:12px; margin-left:0px; margin-right:0px; -qt-block-indent:0; text-indent:0px;\"><a name=\"section7\"></a><span style=\" font-size:medium; font-weight:600;\">7</span><span style=\" font-size:medium; font-weight:600;\">. Additional Terms.</span> </p>\n"
"<p style=\" margin-top:12px; margin-bottom:12px; margin-left:0px; margin-right:0px; -qt-block-indent:0; text-indent:0px;\">“Additional permissions” are terms that supplement the terms of this License by making exceptions from one or more of its conditions. Additional permissions that are applicable to the entire Program shall be treated as though they were included in this License, to the extent that they are valid under applicable law. If additional permissions apply only to part of the Program, that part may be used separately under those permissions, but the entire Program remains governed by this License without regard to the additional permissions. </p>\n"
"<p style=\" margin-top:12px; margin-bottom:12px; margin-left:0px; margin-right:0px; -qt-block-indent:0; text-indent:0px;\">When you convey a copy of a covered work, you may at your option remove any additional permissions from that copy, or from any part of it. (Additional permissions may be written to require their own removal in certain cases when you modify the work.) You may place additional permissions on material, added by you to a covered work, for which you have or can give appropriate copyright permission. </p>\n"
"<p style=\" margin-top:12px; margin-bottom:12px; margin-left:0px; margin-right:0px; -qt-block-indent:0; text-indent:0px;\">Notwithstanding any other provision of this License, for material you add to a covered work, you may (if authorized by the copyright holders of that material) supplement the terms of this License with terms: </p>\n"
"<ul style=\"margin-top: 0px; margin-bottom: 0px; margin-left: 0px; margin-right: 0px; -qt-list-indent: 1;\"><li style=\" margin-top:12px; margin-bottom:0px; margin-left:0px; margin-right:0px; -qt-block-indent:0; text-indent:0px;\">a) Disclaiming warranty or limiting liability differently from the terms of sections 15 and 16 of this License; or </li>\n"
"<li style=\" margin-top:0px; margin-bottom:0px; margin-left:0px; margin-right:0px; -qt-block-indent:0; text-indent:0px;\">b) Requiring preservation of specified reasonable legal notices or author attributions in that material or in the Appropriate Legal Notices displayed by works containing it; or </li>\n"
"<li style=\" margin-top:0px; margin-bottom:0px; margin-left:0px; margin-right:0px; -qt-block-indent:0; text-indent:0px;\">c) Prohibiting misrepresentation of the origin of that material, or requiring that modified versions of such material be marked in reasonable ways as different from the original version; or </li>\n"
"<li style=\" margin-top:0px; margin-bottom:0px; margin-left:0px; margin-right:0px; -qt-block-indent:0; text-indent:0px;\">d) Limiting the use for publicity purposes of names of licensors or authors of the material; or </li>\n"
"<li style=\" margin-top:0px; margin-bottom:0px; margin-left:0px; margin-right:0px; -qt-block-indent:0; text-indent:0px;\">e) Declining to grant rights under trademark law for use of some trade names, trademarks, or service marks; or </li>\n"
"<li style=\" margin-top:0px; margin-bottom:12px; margin-left:0px; margin-right:0px; -qt-block-indent:0; text-indent:0px;\">f) Requiring indemnification of licensors and authors of that material by anyone who conveys the material (or modified versions of it) with contractual assumptions of liability to the recipient, for any liability that these contractual assumptions directly impose on those licensors and authors. </li></ul>\n"
"<p style=\" margin-top:12px; margin-bottom:12px; margin-left:0px; margin-right:0px; -qt-block-indent:0; text-indent:0px;\">All other non-permissive additional terms are considered “further restrictions” within the meaning of section 10. If the Program as you received it, or any part of it, contains a notice stating that it is governed by this License along with a term that is a further restriction, you may remove that term. If a license document contains a further restriction but permits relicensing or conveying under this License, you may add to a covered work material governed by the terms of that license document, provided that the further restriction does not survive such relicensing or conveying. </p>\n"
"<p style=\" margin-top:12px; margin-bottom:12px; margin-left:0px; margin-right:0px; -qt-block-indent:0; text-indent:0px;\">If you add terms to a covered work in accord with this section, you must place, in the relevant source files, a statement of the additional terms that apply to those files, or a notice indicating where to find the applicable terms. </p>\n"
"<p style=\" margin-top:12px; margin-bottom:12px; margin-left:0px; margin-right:0px; -qt-block-indent:0; text-indent:0px;\">Additional terms, permissive or non-permissive, may be stated in the form of a separately written license, or stated as exceptions; the above requirements apply either way. </p>\n"
"<p style=\" margin-top:12px; margin-bottom:12px; margin-left:0px; margin-right:0px; -qt-block-indent:0; text-indent:0px;\"><a name=\"section8\"></a><span style=\" font-size:medium; font-weight:600;\">8</span><span style=\" font-size:medium; font-weight:600;\">. Termination.</span> </p>\n"
"<p style=\" margin-top:12px; margin-bottom:12px; margin-left:0px; margin-right:0px; -qt-block-indent:0; text-indent:0px;\">You may not propagate or modify a covered work except as expressly provided under this License. Any attempt otherwise to propagate or modify it is void, and will automatically terminate your rights under this License (including any patent licenses granted under the third paragraph of section 11). </p>\n"
"<p style=\" margin-top:12px; margin-bottom:12px; margin-left:0px; margin-right:0px; -qt-block-indent:0; text-indent:0px;\">However, if you cease all violation of this License, then your license from a particular copyright holder is reinstated (a) provisionally, unless and until the copyright holder explicitly and finally terminates your license, and (b) permanently, if the copyright holder fails to notify you of the violation by some reasonable means prior to 60 days after the cessation. </p>\n"
"<p style=\" margin-top:12px; margin-bottom:12px; margin-left:0px; margin-right:0px; -qt-block-indent:0; text-indent:0px;\">Moreover, your license from a particular copyright holder is reinstated permanently if the copyright holder notifies you of the violation by some reasonable means, this is the first time you have received notice of violation of this License (for any work) from that copyright holder, and you cure the violation prior to 30 days after your receipt of the notice. </p>\n"
"<p style=\" margin-top:12px; margin-bottom:12px; margin-left:0px; margin-right:0px; -qt-block-indent:0; text-indent:0px;\">Termination of your rights under this section does not terminate the licenses of parties who have received copies or rights from you under this License. If your rights have been terminated and not permanently reinstated, you do not qualify to receive new licenses for the same material under section 10. </p>\n"
"<p style=\" margin-top:12px; margin-bottom:12px; margin-left:0px; margin-right:0px; -qt-block-indent:0; text-indent:0px;\"><a name=\"section9\"></a><span style=\" font-size:medium; font-weight:600;\">9</span><span style=\" font-size:medium; font-weight:600;\">. Acceptance Not Required for Having Copies.</span> </p>\n"
"<p style=\" margin-top:12px; margin-bottom:12px; margin-left:0px; margin-right:0px; -qt-block-indent:0; text-indent:0px;\">You are not required to accept this License in order to receive or run a copy of the Program. Ancillary propagation of a covered work occurring solely as a consequence of using peer-to-peer transmission to receive a copy likewise does not require acceptance. However, nothing other than this License grants you permission to propagate or modify any covered work. These actions infringe copyright if you do not accept this License. Therefore, by modifying or propagating a covered work, you indicate your acceptance of this License to do so. </p>\n"
"<p style=\" margin-top:12px; margin-bottom:12px; margin-left:0px; margin-right:0px; -qt-block-indent:0; text-indent:0px;\"><a name=\"section10\"></a><span style=\" font-size:medium; font-weight:600;\">1</span><span style=\" font-size:medium; font-weight:600;\">0. Automatic Licensing of Downstream Recipients.</span> </p>\n"
"<p style=\" margin-top:12px; margin-bottom:12px; margin-left:0px; margin-right:0px; -qt-block-indent:0; text-indent:0px;\">Each time you convey a covered work, the recipient automatically receives a license from the original licensors, to run, modify and propagate that work, subject to this License. You are not responsible for enforcing compliance by third parties with this License. </p>\n"
"<p style=\" margin-top:12px; margin-bottom:12px; margin-left:0px; margin-right:0px; -qt-block-indent:0; text-indent:0px;\">An “entity transaction” is a transaction transferring control of an organization, or substantially all assets of one, or subdividing an organization, or merging organizations. If propagation of a covered work results from an entity transaction, each party to that transaction who receives a copy of the work also receives whatever licenses to the work the party\'s predecessor in interest had or could give under the previous paragraph, plus a right to possession of the Corresponding Source of the work from the predecessor in interest, if the predecessor has it or can get it with reasonable efforts. </p>\n"
"<p style=\" margin-top:12px; margin-bottom:12px; margin-left:0px; margin-right:0px; -qt-block-indent:0; text-indent:0px;\">You may not impose any further restrictions on the exercise of the rights granted or affirmed under this License. For example, you may not impose a license fee, royalty, or other charge for exercise of rights granted under this License, and you may not initiate litigation (including a cross-claim or counterclaim in a lawsuit) alleging that any patent claim is infringed by making, using, selling, offering for sale, or importing the Program or any portion of it. </p>\n"
"<p style=\" margin-top:12px; margin-bottom:12px; margin-left:0px; margin-right:0px; -qt-block-indent:0; text-indent:0px;\"><a name=\"section11\"></a><span style=\" font-size:medium; font-weight:600;\">1</span><span style=\" font-size:medium; font-weight:600;\">1. Patents.</span> </p>\n"
"<p style=\" margin-top:12px; margin-bottom:12px; margin-left:0px; margin-right:0px; -qt-block-indent:0; text-indent:0px;\">A “contributor” is a copyright holder who authorizes use under this License of the Program or a work on which the Program is based. The work thus licensed is called the contributor\'s “contributor version”. </p>\n"
"<p style=\" margin-top:12px; margin-bottom:12px; margin-left:0px; margin-right:0px; -qt-block-indent:0; text-indent:0px;\">A contributor\'s “essential patent claims” are all patent claims owned or controlled by the contributor, whether already acquired or hereafter acquired, that would be infringed by some manner, permitted by this License, of making, using, or selling its contributor version, but do not include claims that would be infringed only as a consequence of further modification of the contributor version. For purposes of this definition, “control” includes the right to grant patent sublicenses in a manner consistent with the requirements of this License. </p>\n"
"<p style=\" margin-top:12px; margin-bottom:12px; margin-left:0px; margin-right:0px; -qt-block-indent:0; text-indent:0px;\">Each contributor grants you a non-exclusive, worldwide, royalty-free patent license under the contributor\'s essential patent claims, to make, use, sell, offer for sale, import and otherwise run, modify and propagate the contents of its contributor version. </p>\n"
"<p style=\" margin-top:12px; margin-bottom:12px; margin-left:0px; margin-right:0px; -qt-block-indent:0; text-indent:0px;\">In the following three paragraphs, a “patent license” is any express agreement or commitment, however denominated, not to enforce a patent (such as an express permission to practice a patent or covenant not to sue for patent infringement). To “grant” such a patent license to a party means to make such an agreement or commitment not to enforce a patent against the party. </p>\n"
"<p style=\" margin-top:12px; margin-bottom:12px; margin-left:0px; margin-right:0px; -qt-block-indent:0; text-indent:0px;\">If you convey a covered work, knowingly relying on a patent license, and the Corresponding Source of the work is not available for anyone to copy, free of charge and under the terms of this License, through a publicly available network server or other readily accessible means, then you must either (1) cause the Corresponding Source to be so available, or (2) arrange to deprive yourself of the benefit of the patent license for this particular work, or (3) arrange, in a manner consistent with the requirements of this License, to extend the patent license to downstream recipients. “Knowingly relying” means you have actual knowledge that, but for the patent license, your conveying the covered work in a country, or your recipient\'s use of the covered work in a country, would infringe one or more identifiable patents in that country that you have reason to believe are valid. </p>\n"
"<p style=\" margin-top:12px; margin-bottom:12px; margin-left:0px; margin-right:0px; -qt-block-indent:0; text-indent:0px;\">If, pursuant to or in connection with a single transaction or arrangement, you convey, or propagate by procuring conveyance of, a covered work, and grant a patent license to some of the parties receiving the covered work authorizing them to use, propagate, modify or convey a specific copy of the covered work, then the patent license you grant is automatically extended to all recipients of the covered work and works based on it. </p>\n"
"<p style=\" margin-top:12px; margin-bottom:12px; margin-left:0px; margin-right:0px; -qt-block-indent:0; text-indent:0px;\">A patent license is “discriminatory” if it does not include within the scope of its coverage, prohibits the exercise of, or is conditioned on the non-exercise of one or more of the rights that are specifically granted under this License. You may not convey a covered work if you are a party to an arrangement with a third party that is in the business of distributing software, under which you make payment to the third party based on the extent of your activity of conveying the work, and under which the third party grants, to any of the parties who would receive the covered work from you, a discriminatory patent license (a) in connection with copies of the covered work conveyed by you (or copies made from those copies), or (b) primarily for and in connection with specific products or compilations that contain the covered work, unless you entered into that arrangement, or that patent license was granted, prior to 28 March 2007. </p>\n"
"<p style=\" margin-top:12px; margin-bottom:12px; margin-left:0px; margin-right:0px; -qt-block-indent:0; text-indent:0px;\">Nothing in this License shall be construed as excluding or limiting any implied license or other defenses to infringement that may otherwise be available to you under applicable patent law. </p>\n"
"<p style=\" margin-top:12px; margin-bottom:12px; margin-left:0px; margin-right:0px; -qt-block-indent:0; text-indent:0px;\"><a name=\"section12\"></a><span style=\" font-size:medium; font-weight:600;\">1</span><span style=\" font-size:medium; font-weight:600;\">2. No Surrender of Others\' Freedom.</span> </p>\n"
"<p style=\" margin-top:12px; margin-bottom:12px; margin-left:0px; margin-right:0px; -qt-block-indent:0; text-indent:0px;\">If conditions are imposed on you (whether by court order, agreement or otherwise) that contradict the conditions of this License, they do not excuse you from the conditions of this License. If you cannot convey a covered work so as to satisfy simultaneously your obligations under this License and any other pertinent obligations, then as a consequence you may not convey it at all. For example, if you agree to terms that obligate you to collect a royalty for further conveying from those to whom you convey the Program, the only way you could satisfy both those terms and this License would be to refrain entirely from conveying the Program. </p>\n"
"<p style=\" margin-top:12px; margin-bottom:12px; margin-left:0px; margin-right:0px; -qt-block-indent:0; text-indent:0px;\"><a name=\"section13\"></a><span style=\" font-size:medium; font-weight:600;\">1</span><span style=\" font-size:medium; font-weight:600;\">3. Use with the GNU Affero General Public License.</span> </p>\n"
"<p style=\" margin-top:12px; margin-bottom:12px; margin-left:0px; margin-right:0px; -qt-block-indent:0; text-indent:0px;\">Notwithstanding any other provision of this License, you have permission to link or combine any covered work with a work licensed under version 3 of the GNU Affero General Public License into a single combined work, and to convey the resulting work. The terms of this License will continue to apply to the part which is the covered work, but the special requirements of the GNU Affero General Public License, section 13, concerning interaction through a network will apply to the combination as such. </p>\n"
"<p style=\" margin-top:12px; margin-bottom:12px; margin-left:0px; margin-right:0px; -qt-block-indent:0; text-indent:0px;\"><a name=\"section14\"></a><span style=\" font-size:medium; font-weight:600;\">1</span><span style=\" font-size:medium; font-weight:600;\">4. Revised Versions of this License.</span> </p>\n"
"<p style=\" margin-top:12px; margin-bottom:12px; margin-left:0px; margin-right:0px; -qt-block-indent:0; text-indent:0px;\">The Free Software Foundation may publish revised and/or new versions of the GNU General Public License from time to time. Such new versions will be similar in spirit to the present version, but may differ in detail to address new problems or concerns. </p>\n"
"<p style=\" margin-top:12px; margin-bottom:12px; margin-left:0px; margin-right:0px; -qt-block-indent:0; text-indent:0px;\">Each version is given a distinguishing version number. If the Program specifies that a certain numbered version of the GNU General Public License “or any later version” applies to it, you have the option of following the terms and conditions either of that numbered version or of any later version published by the Free Software Foundation. If the Program does not specify a version number of the GNU General Public License, you may choose any version ever published by the Free Software Foundation. </p>\n"
"<p style=\" margin-top:12px; margin-bottom:12px; margin-left:0px; margin-right:0px; -qt-block-indent:0; text-indent:0px;\">If the Program specifies that a proxy can decide which future versions of the GNU General Public License can be used, that proxy\'s public statement of acceptance of a version permanently authorizes you to choose that version for the Program. </p>\n"
"<p style=\" margin-top:12px; margin-bottom:12px; margin-left:0px; margin-right:0px; -qt-block-indent:0; text-indent:0px;\">Later license versions may give you additional or different permissions. However, no additional obligations are imposed on any author or copyright holder as a result of your choosing to follow a later version. </p>\n"
"<p style=\" margin-top:12px; margin-bottom:12px; margin-left:0px; margin-right:0px; -qt-block-indent:0; text-indent:0px;\"><a name=\"section15\"></a><span style=\" font-size:medium; font-weight:600;\">1</span><span style=\" font-size:medium; font-weight:600;\">5. Disclaimer of Warranty.</span> </p>\n"
"<p style=\" margin-top:12px; margin-bottom:12px; margin-left:0px; margin-right:0px; -qt-block-indent:0; text-indent:0px;\">THERE IS NO WARRANTY FOR THE PROGRAM, TO THE EXTENT PERMITTED BY APPLICABLE LAW. EXCEPT WHEN OTHERWISE STATED IN WRITING THE COPYRIGHT HOLDERS AND/OR OTHER PARTIES PROVIDE THE PROGRAM “AS IS” WITHOUT WARRANTY OF ANY KIND, EITHER EXPRESSED OR IMPLIED, INCLUDING, BUT NOT LIMITED TO, THE IMPLIED WARRANTIES OF MERCHANTABILITY AND FITNESS FOR A PARTICULAR PURPOSE. THE ENTIRE RISK AS TO THE QUALITY AND PERFORMANCE OF THE PROGRAM IS WITH YOU. SHOULD THE PROGRAM PROVE DEFECTIVE, YOU ASSUME THE COST OF ALL NECESSARY SERVICING, REPAIR OR CORRECTION. </p>\n"
"<p style=\" margin-top:12px; margin-bottom:12px; margin-left:0px; margin-right:0px; -qt-block-indent:0; text-indent:0px;\"><a name=\"section16\"></a><span style=\" font-size:medium; font-weight:600;\">1</span><span style=\" font-size:medium; font-weight:600;\">6. Limitation of Liability.</span> </p>\n"
"<p style=\" margin-top:12px; margin-bottom:12px; margin-left:0px; margin-right:0px; -qt-block-indent:0; text-indent:0px;\">IN NO EVENT UNLESS REQUIRED BY APPLICABLE LAW OR AGREED TO IN WRITING WILL ANY COPYRIGHT HOLDER, OR ANY OTHER PARTY WHO MODIFIES AND/OR CONVEYS THE PROGRAM AS PERMITTED ABOVE, BE LIABLE TO YOU FOR DAMAGES, INCLUDING ANY GENERAL, SPECIAL, INCIDENTAL OR CONSEQUENTIAL DAMAGES ARISING OUT OF THE USE OR INABILITY TO USE THE PROGRAM (INCLUDING BUT NOT LIMITED TO LOSS OF DATA OR DATA BEING RENDERED INACCURATE OR LOSSES SUSTAINED BY YOU OR THIRD PARTIES OR A FAILURE OF THE PROGRAM TO OPERATE WITH ANY OTHER PROGRAMS), EVEN IF SUCH HOLDER OR OTHER PARTY HAS BEEN ADVISED OF THE POSSIBILITY OF SUCH DAMAGES. </p>\n"
"<p style=\" margin-top:12px; margin-bottom:12px; margin-left:0px; margin-right:0px; -qt-block-indent:0; text-indent:0px;\"><a name=\"section17\"></a><span style=\" font-size:medium; font-weight:600;\">1</span><span style=\" font-size:medium; font-weight:600;\">7. Interpretation of Sections 15 and 16.</span> </p>\n"
"<p style=\" margin-top:12px; margin-bottom:12px; margin-left:0px; margin-right:0px; -qt-block-indent:0; text-indent:0px;\">If the disclaimer of warranty and limitation of liability provided above cannot be given local legal effect according to their terms, reviewing courts shall apply local law that most closely approximates an absolute waiver of all civil liability in connection with the Program, unless a warranty or assumption of liability accompanies a copy of the Program in return for a fee. </p>\n"
"<p style=\" margin-top:12px; margin-bottom:12px; margin-left:0px; margin-right:0px; -qt-block-indent:0; text-indent:0px;\">END OF TERMS AND CONDITIONS </p>\n"
"<p style=\" margin-top:14px; margin-bottom:12px; margin-left:0px; margin-right:0px; -qt-block-indent:0; text-indent:0px;\"><a name=\"howto\"></a><span style=\" font-size:large; font-weight:600;\">H</span><span style=\" font-size:large; font-weight:600;\">ow to Apply These Terms to Your New Programs</span> </p>\n"
"<p style=\" margin-top:12px; margin-bottom:12px; margin-left:0px; margin-right:0px; -qt-block-indent:0; text-indent:0px;\">If you develop a new program, and you want it to be of the greatest possible use to the public, the best way to achieve this is to make it free software which everyone can redistribute and change under these terms. </p>\n"
"<p style=\" margin-top:12px; margin-bottom:12px; margin-left:0px; margin-right:0px; -qt-block-indent:0; text-indent:0px;\">To do so, attach the following notices to the program. It is safest to attach them to the start of each source file to most effectively state the exclusion of warranty; and each file should have at least the “copyright” line and a pointer to where the full notice is found. </p>\n"
"<p style=\" margin-top:12px; margin-bottom:0px; margin-left:0px; margin-right:0px; -qt-block-indent:0; text-indent:0px;\"><span style=\" font-family:\'Courier New,courier\';\">    &lt;one line to give the program\'s name and a brief idea of what it does.&gt;</span></p>\n"
"<p style=\" margin-top:0px; margin-bottom:0px; margin-left:0px; margin-right:0px; -qt-block-indent:0; text-indent:0px;\"><span style=\" font-family:\'Courier New,courier\';\">    Copyright (C) &lt;year&gt;  &lt;name of author&gt;</span></p>\n"
"<p style=\"-qt-paragraph-type:empty; margin-top:0px; margin-bottom:0px; margin-left:0px; margin-right:0px; -qt-block-indent:0; text-indent:0px; font-family:\'Courier New,courier\';\"><br /></p>\n"
"<p style=\" margin-top:0px; margin-bottom:0px; margin-left:0px; margin-right:0px; -qt-block-indent:0; text-indent:0px;\"><span style=\" font-family:\'Courier New,courier\';\">    This program is free software: you can redistribute it and/or modify</span></p>\n"
"<p style=\" margin-top:0px; margin-bottom:0px; margin-left:0px; margin-right:0px; -qt-block-indent:0; text-indent:0px;\"><span style=\" font-family:\'Courier New,courier\';\">    it under the terms of the GNU General Public License as published by</span></p>\n"
"<p style=\" margin-top:0px; margin-bottom:0px; margin-left:0px; margin-right:0px; -qt-block-indent:0; text-indent:0px;\"><span style=\" font-family:\'Courier New,courier\';\">    the Free Software Foundation, either version 3 of the License, or</span></p>\n"
"<p style=\" margin-top:0px; margin-bottom:0px; margin-left:0px; margin-right:0px; -qt-block-indent:0; text-indent:0px;\"><span style=\" font-family:\'Courier New,courier\';\">    (at your option) any later version.</span></p>\n"
"<p style=\"-qt-paragraph-type:empty; margin-top:0px; margin-bottom:0px; margin-left:0px; margin-right:0px; -qt-block-indent:0; text-indent:0px; font-family:\'Courier New,courier\';\"><br /></p>\n"
"<p style=\" margin-top:0px; margin-bottom:0px; margin-left:0px; margin-right:0px; -qt-block-indent:0; text-indent:0px;\"><span style=\" font-family:\'Courier New,courier\';\">    This program is distributed in the hope that it will be useful,</span></p>\n"
"<p style=\" margin-top:0px; margin-bottom:0px; margin-left:0px; margin-right:0px; -qt-block-indent:0; text-indent:0px;\"><span style=\" font-family:\'Courier New,courier\';\">    but WITHOUT ANY WARRANTY; without even the implied warranty of</span></p>\n"
"<p style=\" margin-top:0px; margin-bottom:0px; margin-left:0px; margin-right:0px; -qt-block-indent:0; text-indent:0px;\"><span style=\" font-family:\'Courier New,courier\';\">    MERCHANTABILITY or FITNESS FOR A PARTICULAR PURPOSE.  See the</span></p>\n"
"<p style=\" margin-top:0px; margin-bottom:0px; margin-left:0px; margin-right:0px; -qt-block-indent:0; text-indent:0px;\"><span style=\" font-family:\'Courier New,courier\';\">    GNU General Public License for more details.</span></p>\n"
"<p style=\"-qt-paragraph-type:empty; margin-top:0px; margin-bottom:0px; margin-left:0px; margin-right:0px; -qt-block-indent:0; text-indent:0px; font-family:\'Courier New,courier\';\"><br /></p>\n"
"<p style=\" margin-top:0px; margin-bottom:0px; margin-left:0px; margin-right:0px; -qt-block-indent:0; text-indent:0px;\"><span style=\" font-family:\'Courier New,courier\';\">    You should have received a copy of the GNU General Public License</span></p>\n"
"<p style=\" margin-top:0px; margin-bottom:12px; margin-left:0px; margin-right:0px; -qt-block-indent:0; text-indent:0px;\"><span style=\" font-family:\'Courier New,courier\';\">    along with this program.  If not, see &lt;http://www.gnu.org/licenses/&gt;. </span></p>\n"
"<p style=\" margin-top:12px; margin-bottom:12px; margin-left:0px; margin-right:0px; -qt-block-indent:0; text-indent:0px;\">Also add information on how to contact you by electronic and paper mail. </p>\n"
"<p style=\" margin-top:12px; margin-bottom:12px; margin-left:0px; margin-right:0px; -qt-block-indent:0; text-indent:0px;\">If the program does terminal interaction, make it output a short notice like this when it starts in an interactive mode: </p>\n"
"<p style=\" margin-top:12px; margin-bottom:0px; margin-left:0px; margin-right:0px; -qt-block-indent:0; text-indent:0px;\"><span style=\" font-family:\'Courier New,courier\';\">    &lt;program&gt;  Copyright (C) &lt;year&gt;  &lt;name of author&gt;</span></p>\n"
"<p style=\" margin-top:0px; margin-bottom:0px; margin-left:0px; margin-right:0px; -qt-block-indent:0; text-indent:0px;\"><span style=\" font-family:\'Courier New,courier\';\">    This program comes with ABSOLUTELY NO WARRANTY; for details type `show w\'.</span></p>\n"
"<p style=\" margin-top:0px; margin-bottom:0px; margin-left:0px; margin-right:0px; -qt-block-indent:0; text-indent:0px;\"><span style=\" font-family:\'Courier New,courier\';\">    This is free software, and you are welcome to redistribute it</span></p>\n"
"<p style=\" margin-top:0px; margin-bottom:12px; margin-left:0px; margin-right:0px; -qt-block-indent:0; text-indent:0px;\"><span style=\" font-family:\'Courier New,courier\';\">    under certain conditions; type `show c\' for details. </span></p>\n"
"<p style=\" margin-top:12px; margin-bottom:12px; margin-left:0px; margin-right:0px; -qt-block-indent:0; text-indent:0px;\">The hypothetical commands `show w\' and `show c\' should show the appropriate parts of the General Public License. Of course, your program\'s commands might be different; for a GUI interface, you would use an “about box”. </p>\n"
"<p style=\" margin-top:12px; margin-bottom:12px; margin-left:0px; margin-right:0px; -qt-block-indent:0; text-indent:0px;\">You should also get your employer (if you work as a programmer) or school, if any, to sign a “copyright disclaimer” for the program, if necessary. For more information on this, and how to apply and follow the GNU GPL, see &lt;<a href=\"http://www.gnu.org/licenses/\"><span style=\" text-decoration: underline; color:#0000ff;\">http://www.gnu.org/licenses/</span></a>&gt;. </p>\n"
"<p style=\" margin-top:12px; margin-bottom:12px; margin-left:0px; margin-right:0px; -qt-block-indent:0; text-indent:0px;\">The GNU General Public License does not permit incorporating your program into proprietary programs. If your program is a subroutine library, you may consider it more useful to permit linking proprietary applications with the library. If this is what you want to do, use the GNU Lesser General Public License instead of this License. But first, please read &lt;<a href=\"http://www.gnu.org/philosophy/why-not-lgpl.html\"><span style=\" text-decoration: underline; color:#0000ff;\">http://www.gnu.org/philosophy/why-not-lgpl.html</span></a>&gt;. </p></body></html>"))
        self.aboutQt.setText(_translate("MainWindow", "À propos de Qt"))
        self.tabWidget_2.setTabText(self.tabWidget_2.indexOf(self.tab_4), _translate("MainWindow", "À propos de cette application"))
        self.actionSave.setText(_translate("MainWindow", "Save"))
        self.actionSave.setShortcut(_translate("MainWindow", "Ctrl+S"))
        self.actionSaveAs.setText(_translate("MainWindow", "SaveAs"))
        self.actionSaveAs.setShortcut(_translate("MainWindow", "Ctrl+Shift+S"))
        self.actionRedraw.setText(_translate("MainWindow", "Redraw"))
        self.actionRedraw.setShortcut(_translate("MainWindow", "Ctrl+D"))
        self.actionReload.setText(_translate("MainWindow", "Reload"))
        self.actionReload.setShortcut(_translate("MainWindow", "Ctrl+R"))
