Klafyvel/Trace/Trace/codes.h

#define UNKN 0
#define G00 1
#define G01 2
#define G02 3
#define G03 4
#define G04 5
#define G05 6
#define G06 7
#define G07 8
#define G08 9
#define G09 10
#define G10 11
#define G11 12
#define G12 13
#define G13 14
#define G14 15
#define G15 16
#define G16 17
#define G17 18
#define G18 19
#define G19 20
#define G20 21
#define G21 22
#define G22 23
#define G23 24
#define G24 25
#define G25 26
#define G26 27
#define G27 28
#define G28 29
#define G29 30
#define G30 31
#define G31 32
#define G32 33
#define G33 34
#define G34 35
#define G35 36
#define G36 37
#define G37 38
#define G38 39
#define G39 40
#define G40 41
#define G41 42
#define G42 43
#define G43 44
#define G44 45
#define G45 46
#define G46 47
#define G47 48
#define G48 49
#define G49 50
#define G50 51
#define G51 52
#define G52 53
#define G53 54
#define G54 55
#define G55 56
#define G56 57
#define G57 58
#define G58 59
#define G59 60
#define G60 61
#define G61 62
#define G62 63
#define G63 64
#define G64 65
#define G65 66
#define G66 67
#define G67 68
#define G68 69
#define G69 70
#define G70 71
#define G71 72
#define G72 73
#define G73 74
#define G74 75
#define G75 76
#define G76 77
#define G77 78
#define G78 79
#define G79 80
#define G80 81
#define G81 82
#define G82 83
#define G83 84
#define G84 85
#define G85 86
#define G86 87
#define G87 88
#define G88 89
#define G89 90
#define G90 91
#define G91 92
#define G92 93
#define G93 94
#define G94 95
#define G95 96
#define G96 97
#define G97 98
#define G98 99
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
#define M82 182
#define M83 183
#define M84 184
#define M85 185
#define M86 186
#define M87 187
#define M88 188
#define M89 189
#define M90 190
#define M91 191
#define M92 192
#define M93 193
#define M94 194
#define M95 195
#define M96 196
#define M97 197
#define M98 198
#define M99 199
